magkosm/ENV_sensors_project/1-Mechanical/Version 1/IMG/Isometric.PNG

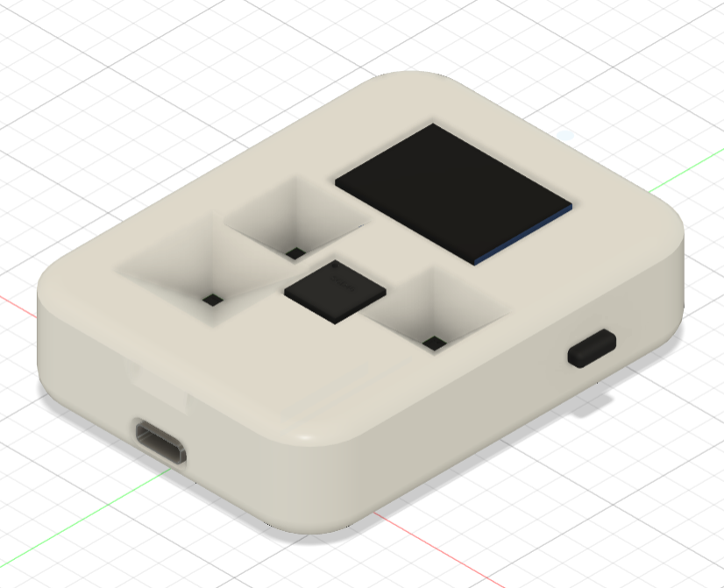
1-Mechanical/Version 1/IMG/Isometric.PNG
