magkosm/ENV_sensors_project/1-Mechanical/Version 2 (Not Fisnished)/IMG/Isometric.PNG

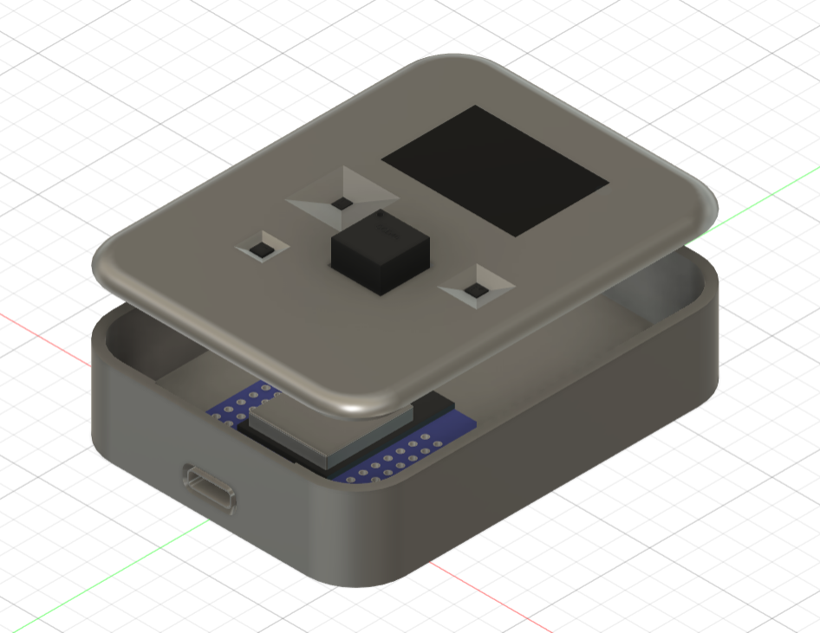
1-Mechanical/Version 2 (Not Fisnished)/IMG/Isometric.PNG
