magkosm/ENV_sensors_project/2-Electronics/PCB/Version 3/Images/PCB Scheme.PNG

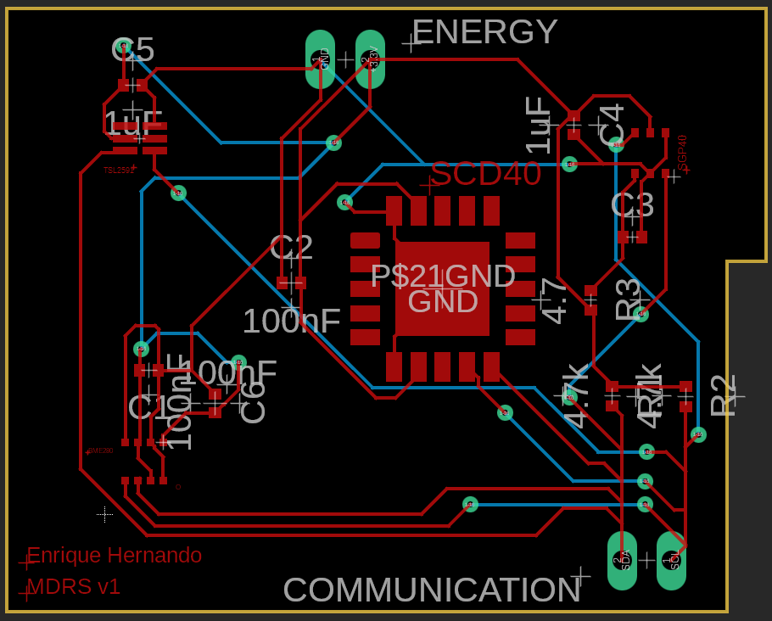
2-Electronics/PCB/Version 3/Images/PCB Scheme.PNG
